OBU5/PPM_nucleo/SW/PC-DataAcquisition-Python/PPM_dataAnalysis/generatedFiles/figures/1extADC.png

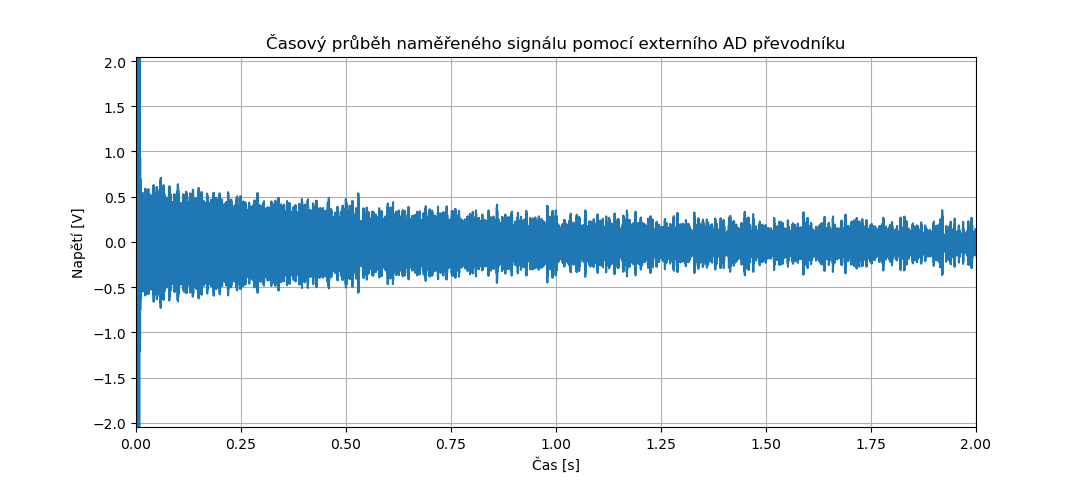
SW/PC-DataAcquisition-Python/PPM_dataAnalysis/generatedFiles/figures/1extADC.png
