OBU5/PPM_nucleo/SW/PC-DataAcquisition-Python/PPM_dataAnalysis/generatedFiles/figures/3extADC.png

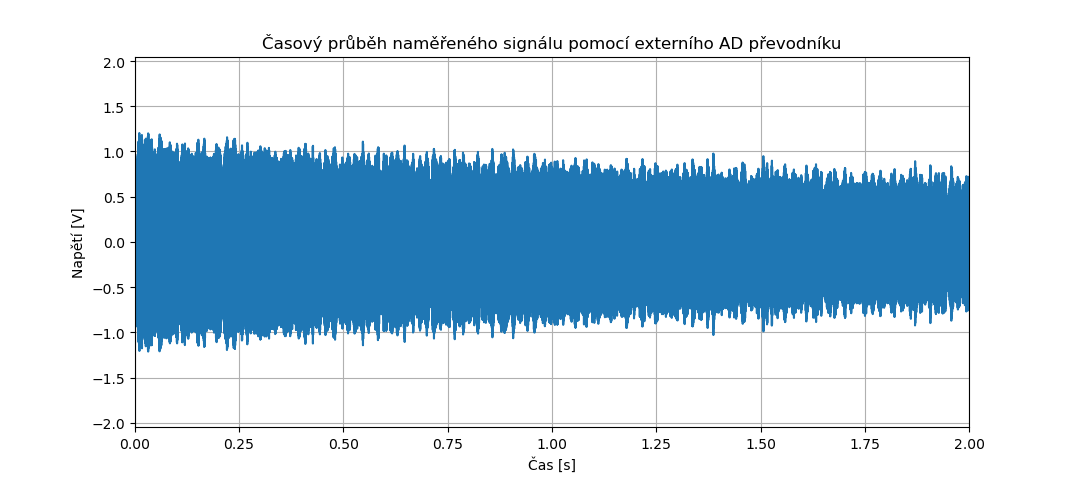
SW/PC-DataAcquisition-Python/PPM_dataAnalysis/generatedFiles/figures/3extADC.png
