OBU5/PPM_nucleo/SW/PC-DataAcquisition-Python/PPM_dataAnalysis/generatedFiles/figures/6extADC_hilbert.png

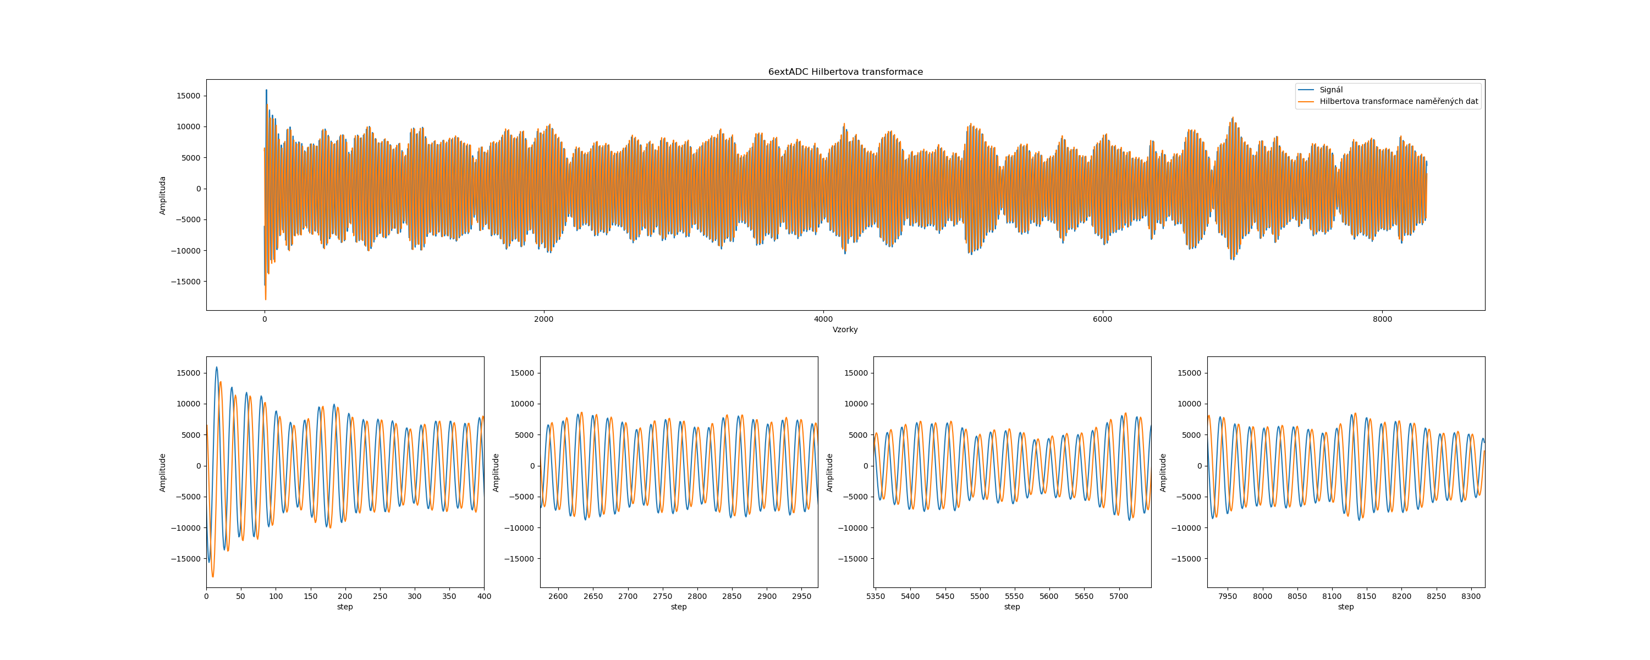
SW/PC-DataAcquisition-Python/PPM_dataAnalysis/generatedFiles/figures/6extADC_hilbert.png
