OBU5/PPM_nucleo/SW/PC-DataAcquisition-Python/PPM_dataAnalysis/generatedFiles/figures/4extADC_reconstructed.png

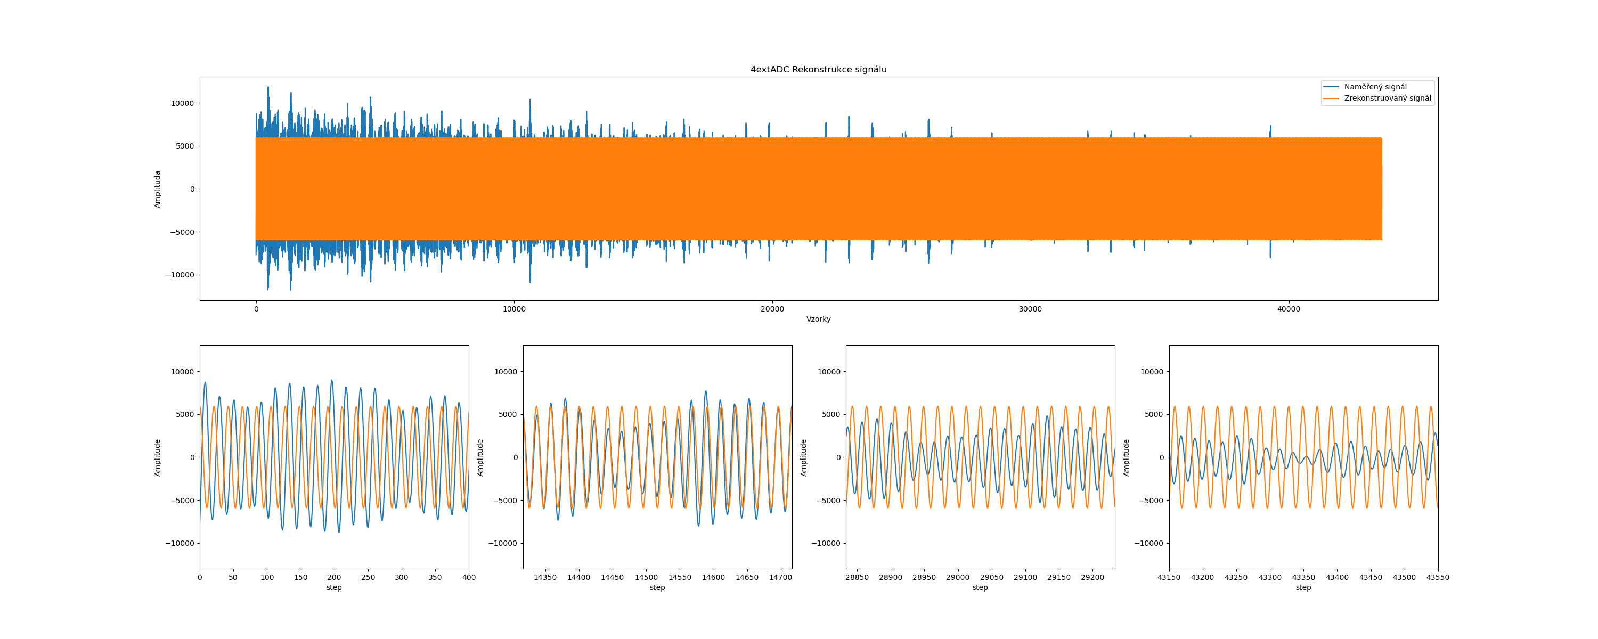
SW/PC-DataAcquisition-Python/PPM_dataAnalysis/generatedFiles/figures/4extADC_reconstructed.png
