OBU5/PPM_nucleo/SW/PC-DataAcquisition-Python/PPM_dataAnalysis/other/test copy.txt

<MEAS:4:extADC:
32521
32375
51607
57302
60827
61921
60426
56487
50421
42726
34090
25259
17025
10131
5203
2717
2901
5758
11105
18402
27058
36268
45225
53118
59232
63027
64151
62529
58220
51654
43382
34108
24616
15775
8327
2959
144
163
3031
8533
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
