OBU5/PPM_nucleo/SW/PC-DataAcquisition-Python/PPM_dataAnalysis/generatedFiles/OldMeasurements/results_meas1_250ms.csv

time | hilbert transform | fft without zero padding | fft with zero padding (441000) | fft with zero padding (4410000) | comparator
0 | 49151.45318758884 | 49167.52790752812 | 49148.155606591026 | 49148.105173841854 | 49152.75769464838
8 | 49142.50312793602 | 49167.52790752812 | 49146.984095855 | 49148.105173841854 | 49138.4617357453
16 | 49144.71157001659 | 49167.52790752812 | 49149.32711732706 | 49150.39881324702 | 49162.654948598436
24 | 49145.038356751036 | 49167.52790752812 | 49147.452700149406 | 49148.105173841854 | 49150.44881182785
32 | 49138.85560916981 | 49167.52790752812 | 49150.03002376868 | 49150.39881324702 | 49157.837077241624
40 | 49149.69101414506 | 49167.52790752812 | 49148.85851303265 | 49148.105173841854 | 49152.601289310194
48 | 49149.88136577044 | 49167.52790752812 | 49149.79572162147 | 49150.39881324702 | 49147.77783332824
56 | 49139.56761218177 | 49167.52790752812 | 49147.2183980022 | 49148.105173841854 | 49148.560361517026
64 | 49144.832647829 | 49167.52790752812 | 49147.92130444382 | 49148.105173841854 | 49152.6862387278
72 | 49144.423158066136 | 49167.52790752812 | 49146.28118941338 | 49145.81153443669 | 49143.60098857365
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
