OBU5/PPM_nucleo/SW/PC-DataAcquisition-Python/PPM_dataAnalysis/generatedFiles/OldMeasurements/results_meas1_500ms.csv

time | hilbert transform | fft without zero padding | fft witho zero padding (441000) | fft witho zero padding (4410000) | comparator
0 | 49146.514568066435 | 49150.183784552784 | 49146.24951056396 | 49145.5192515942 | 49147.74680069883
4 | 49148.919762579746 | 49150.183784552784 | 49147.18438755141 | 49147.75822741432 | 49149.772541487284
8 | 49143.19398862941 | 49150.183784552784 | 49147.18438755141 | 49147.75822741432 | 49151.27889778424
12 | 49143.56378068247 | 49150.183784552784 | 49147.41810679827 | 49147.75822741432 | 49148.01716465116
16 | 49096.086733323245 | 49150.183784552784 | 49148.58670303257 | 49147.75822741432 | 49136.11168052352
20 | 49146.15417091074 | 49150.183784552784 | 49148.82042227942 | 49147.75822741432 | 49139.6753882952
24 | 49143.181646345656 | 49150.183784552784 | 49149.05414152629 | 49149.99720323444 | 49140.91483047656
28 | 49145.20078881568 | 49150.183784552784 | 49147.41810679827 | 49147.75822741432 | 49132.253603392484
32 | 49143.69420321747 | 49150.183784552784 | 49147.41810679827 | 49147.75822741432 | 49146.01431017317
36 | 49139.82723169383 | 49150.183784552784 | 49146.95066830454 | 49147.75822741432 | 49144.910242001126
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
