OBU5/PPM_nucleo/SW/PC-DataAcquisition-Python/PPM_dataAnalysis/generatedFiles/OldMeasurements/results_meas1_750ms.csv

time | hilbert transform | fft without zero padding | fft with zero padding (441000) | fft with zero padding (4410000) | comparator
0 | 49145.18458093413 | 49144.56189641593 | 49145.984849706 | 49145.24057621897 | 49127.82710548021
8 | 49147.97337782131 | 49144.56189641593 | 49147.61682438329 | 49147.42743336204 | 49107.006824312004
16 | 49113.895346558216 | 49144.56189641593 | 49146.91740666445 | 49147.42743336204 | 49109.191311859686
24 | 49113.767548735545 | 49144.56189641593 | 49147.38368514367 | 49147.42743336204 | 49104.891080545574
32 | 49084.96175779538 | 49144.56189641593 | 49148.78252058136 | 49149.61429050511 | 49072.562184062714
40 | 49147.368216460374 | 49144.56189641593 | 49148.78252058136 | 49149.61429050511 | 49118.73806307586
48 | 49052.011271924144 | 49144.56189641593 | 49148.78252058136 | 49149.61429050511 | 49097.10587376831
56 | 49082.73855849062 | 49144.56189641593 | 49147.38368514367 | 49147.42743336204 | 49089.89266597615
64 | 49113.08489993714 | 49144.56189641593 | 49147.38368514367 | 49147.42743336204 | 49133.91692677869
72 | 49112.817537380906 | 49144.56189641593 | 49147.150545904056 | 49147.42743336204 | 49123.61486287635
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
