OBU5/PPM_nucleo/SW/PC-DataAcquisition-Python/PPM_dataAnalysis/generatedFiles/OldMeasurements/results_meas2_1000ms.csv

time | hilbert transform | fft without zero padding | fft with zero padding (441000) | fft with zero padding (4410000) | comparator
0 | 49004.97308229994 | 49150.623705642814 | 49145.5755577941 | 49145.770593493944 | 49073.363244880245
8 | 48980.72992696573 | 49150.623705642814 | 49143.482475359786 | 49143.63326329504 | 48996.39168142143
16 | 49003.73942079006 | 49150.623705642814 | 49145.110428364256 | 49145.770593493944 | 49064.28386058848
24 | 49070.88191209912 | 49150.623705642814 | 49146.273251938874 | 49145.770593493944 | 49041.917231479696
32 | 48953.58279550621 | 49150.623705642814 | 49147.4360755135 | 49147.90792369284 | 49003.77839395017
40 | 48904.5355517516 | 49150.623705642814 | 49147.20351079857 | 49147.90792369284 | 49010.943328270994
48 | 49053.14511391361 | 49150.623705642814 | 49150.22685209258 | 49150.04525389174 | 49115.03155163521
56 | 49078.730316159745 | 49150.623705642814 | 49151.389675667204 | 49152.18258409064 | 49081.8453207993
64 | 49020.74993764813 | 49150.623705642814 | 49153.017628671674 | 49152.18258409064 | 49110.65688017938
72 | 49028.897461614586 | 49150.623705642814 | 49152.087369811976 | 49152.18258409064 | 49022.067161686435
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
