OBU5/PPM_nucleo/SW/STM32_PPM/PPM_standalone/Core/Src/switchingCircuitController.h

/*
 * switchingController.h
 *
 *  Created on: Apr 30, 2021
 *      Author: OBU
 */


#include "config.h"
#include"main.h"
#ifndef SRC_SWITCHINGCONTROLLER_H_
#define SRC_SWITCHINGCONTROLLER_H_

void runPolarizationSequence();

void runMeasurementSequence() ;

void switchingCircuitIdle() ;

void switchingCircuitOff();

#endif /* SRC_SWITCHINGCONTROLLER_H_ */
