OBU5/PPM_nucleo/SW/STM32_PPM/PPM_standalone/Core/Src/stateController.h

/*
 * stateController.h
 *
 *  Created on: Apr 30, 2021
 *      Author: OBU
 */

#include "config.h"


#ifndef SRC_STATECONTROLLER_H_
#define SRC_STATECONTROLLER_H_



#endif /* SRC_STATECONTROLLER_H_ */
