OBU5/PPM_nucleo/SW/STM32_PPM/PPM_standalone/Core/Src/gpio.h

#include "main.h"
#include "config.h"

/*
 * gpio.h
 *
 *  Created on: Apr 30, 2021
 *      Author: OBU
 */

#ifndef SRC_GPIO_H_
#define SRC_GPIO_H_


void set_LED1(uint8_t R, uint8_t G, uint8_t B);
void set_LED2(uint8_t val);
void set_LED3(uint8_t val);
void set_LED4(uint8_t val);

void HAL_GPIO_EXTI_Callback(uint16_t GPIO_Pin);
#endif /* SRC_GPIO_H_ */
