OBU5/PPM_nucleo/SW/STM32_PPM/PPM_standalone/Core/Src/delay.h

/*
 * delay.h
 *
 *  Created on: Apr 30, 2021
 *      Author: OBU
 */

#include "config.h"
#include <stdint.h>

#ifndef SRC_DELAY_H_
#define SRC_DELAY_H_

void delay_us(uint32_t delay_us);

void delay_ms(uint32_t delay_us);



#endif /* SRC_DELAY_H_ */
