OBU5/PPM_nucleo/SW/PC-DataAcquisition-Python/PPM_dataAnalysis/other/csvDataAnalysis.py

import csv
# #read data
# with open('test.csv') as csv_file:
#     csv_reader = csv.reader(csv_file, delimiter=',')
#     line_count = 0
#     for row in csv_reader:
#         if line_count == 0:
#             print(f'Column names are {", ".join(row)}')
#             line_count += 1
#         else:
#             print(f'\t{row[0]} works in the {row[1]} department, and was born in {row[2]}.')
#             line_count += 1
#     print(f'Processed {line_count} lines.')


#write data  
with open('test.csv', mode='w') as csvFile:
    csvFileWriter = csv.writer(csvFile, delimiter=',', quotechar='"', lineterminator='\n', quoting=csv.QUOTE_MINIMAL)

    csvFileWriter.writerow(['0', '1234'])
    csvFileWriter.writerow(['1', '12350'])
    csvFileWriter.writerow(['2', '12350'])
    csvFileWriter.writerow(['3', '12350'])
