OBU5/PPM_nucleo/SW/PC-DataAcquisition-Python/PPM_dataAnalysis/other/createPlot-example.py

# importing the required module 
import matplotlib.pyplot as plt 
  
# x axis values 
x = [1,2,3] 
# corresponding y axis values 
y = [2,4,1] 
  
# plotting the points  
plt.plot(x, y) 
  
# naming the x axis 
plt.xlabel('vzorek') 
# naming the y axis 
plt.ylabel('amplituda') 
  
# giving a title to my graph 
plt.title('Amp1') 
  
# function to show the plot 
plt.show() 
